jwebb4/All-Strings-Attached/Old_models/Second model/device housing.SLDPRT

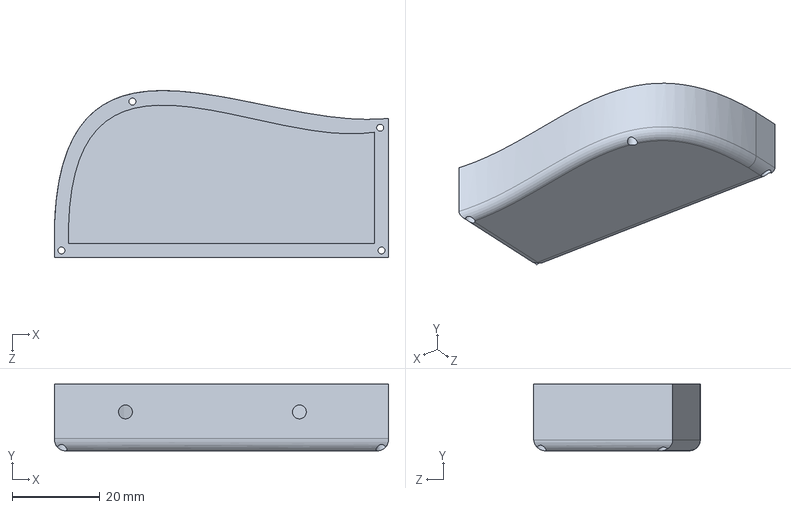
[picture p15: CAD file, 2022-04-01, an earlier design]
Old_models/Second model/device housing.SLDPRT
76.2 x 15.2 x 38.1 mm
