jwebb4/All-Strings-Attached/Old_models/First model/Kim-practice.SLDPRT

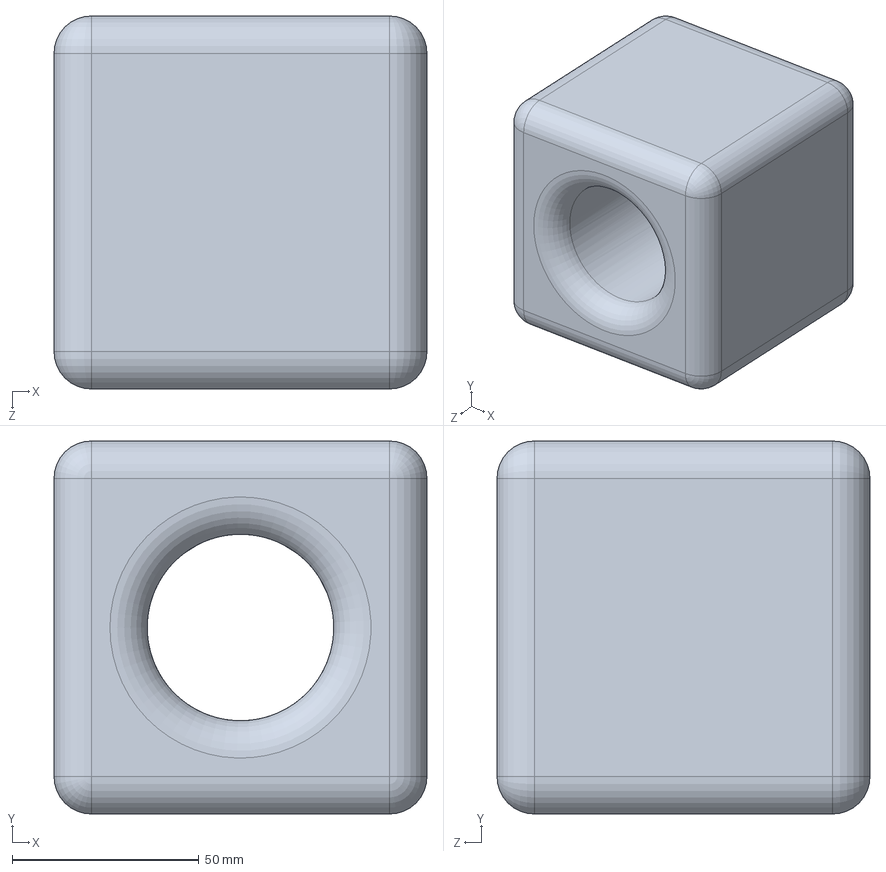
[picture p16: CAD file, 2022-04-01, an earlier design]
Old_models/First model/Kim-practice.SLDPRT
100.0 x 100.0 x 100.0 mm
