jwebb4/All-Strings-Attached/Old_models/Fourth model/Top of device.STL

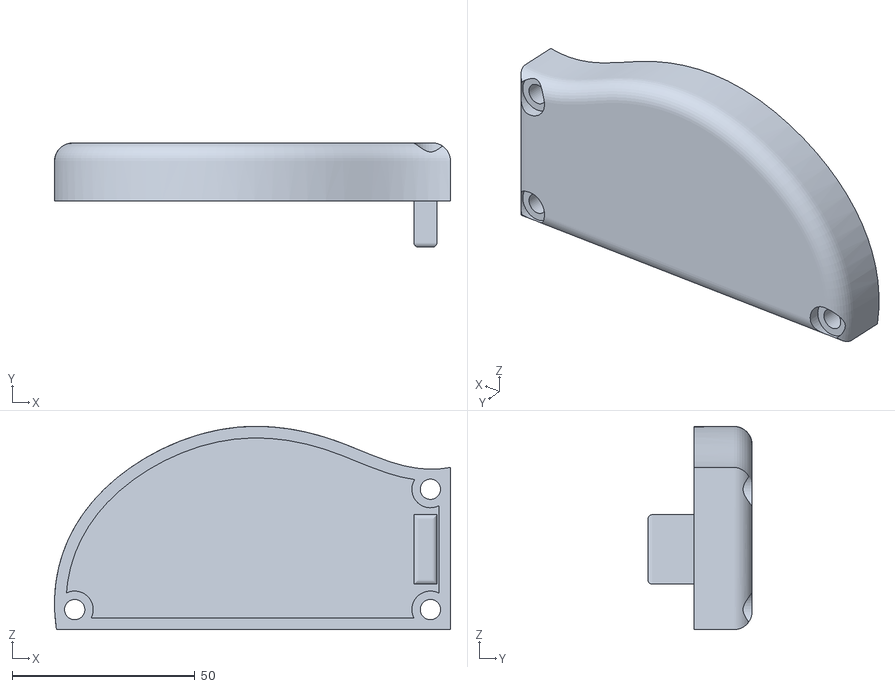
[picture p17: CAD file, 2022-04-01, an earlier design]
Old_models/Fourth model/Top of device.STL
108.5 x 28.6 x 55.7
